Taro-Hayashi/4-input-stereo-mixer/img/IMG_9550.jpeg

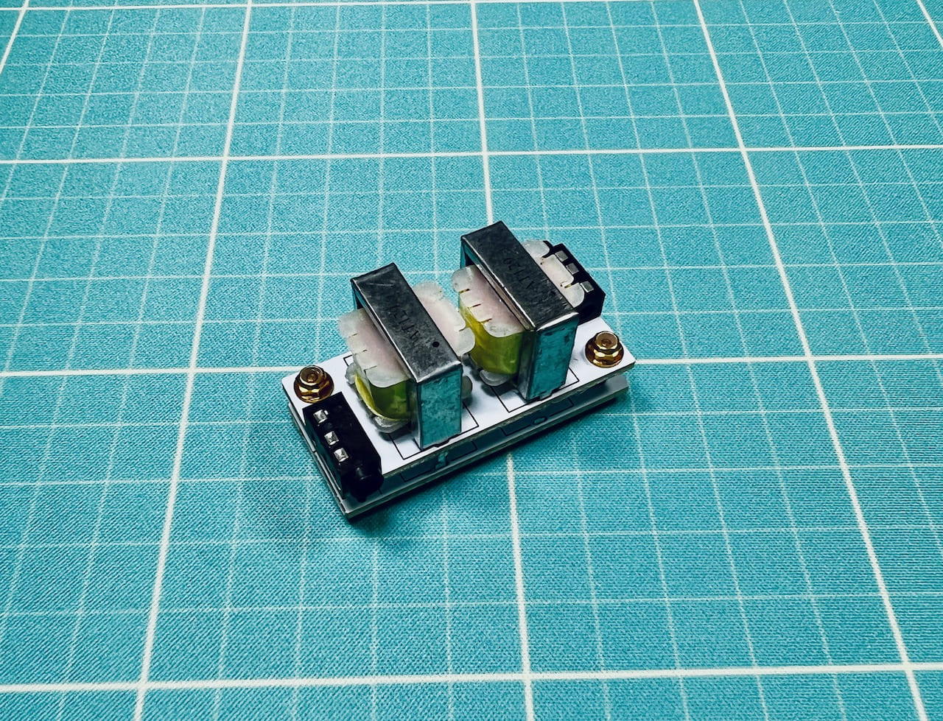
img/IMG_9550.jpeg
